Bert-Tec/xbot_display/serial/01_checkdata_1.jpg

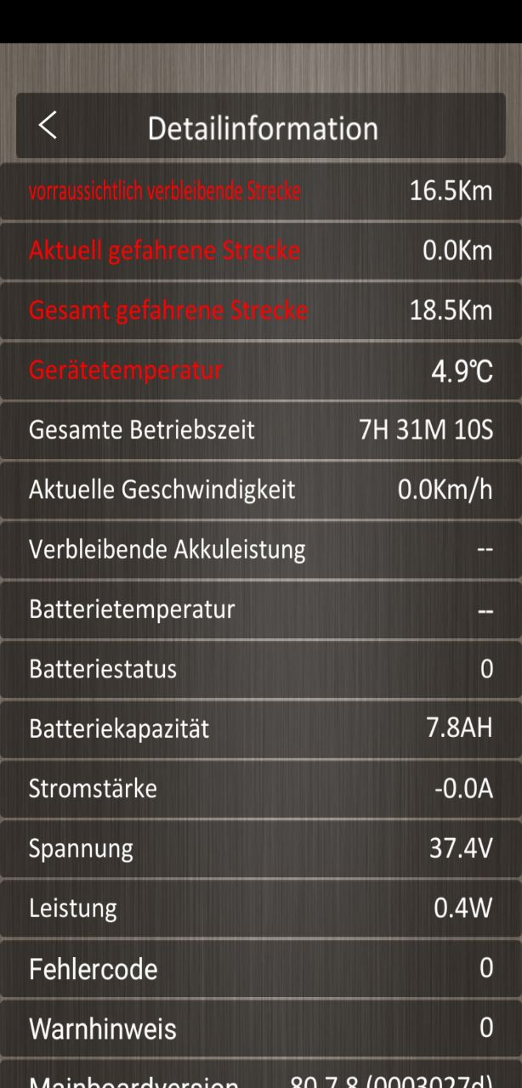
serial/01_checkdata_1.jpg
