Bert-Tec/xbot_display/serial/01_checkdata_2.jpg

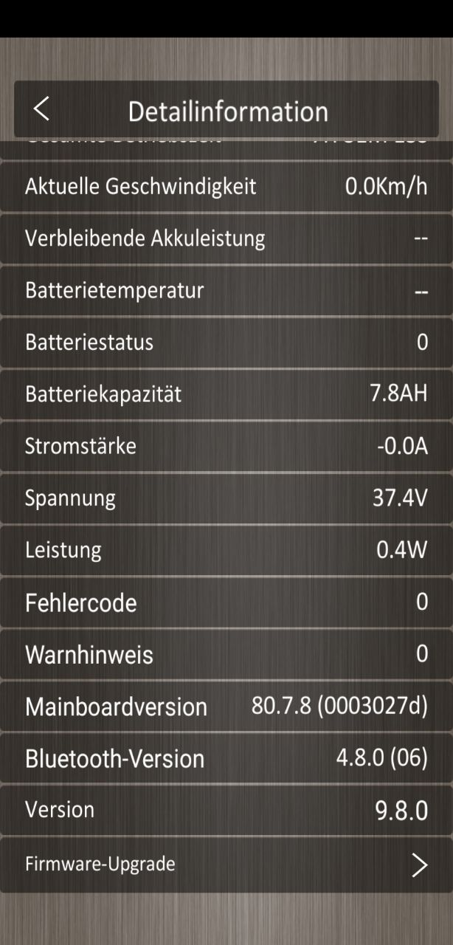
serial/01_checkdata_2.jpg
